Riik/led-matrix/v2/raspberrypi/inc/frameLimiter.hpp

#ifndef FRAMELIMITER_HPP
#define FRAMELIMITER_HPP

#include <chrono>

class FrameLimiter {
    public:
        /* zero is a special case, in that case there will be no sleeping. */
        FrameLimiter(uint_fast32_t framesPerSecond);

        /* Puts the calling thread to sleep until the next frame. */
        void waitForNextFrame();

    private:
        std::chrono::time_point<std::chrono::steady_clock> lastWakeTime;
        std::chrono::nanoseconds timePerFrame;
};

#endif //FRAMELIMITER_HPP
