Riik/led-matrix/v2/raspberrypi/inc/matrixScreen.hpp

#ifndef MATRIXSCREEN_HPP
#define MATRIXSCREEN_HPP
#include <vector>

#include "pixelColor.hpp"

/**
 * The bottom-left is coordinate 0,0.
 */
class MatrixScreen {

    public:
        static constexpr std::size_t matrixPixelCountWidth = 8;
        static constexpr std::size_t matrixPixelCountHeight = 8;

        explicit MatrixScreen(const std::size_t& matrixCountWidth, const std::size_t& matrixCountHeight);

        std::size_t getMatrixCountWidth() const;
        std::size_t getMatrixCountHeight() const;
        std::size_t getPixelCountWidth() const;
        std::size_t getPixelCountHeight() const;

        void resetScreen(PixelColor color);

        PixelColor operator()(std::size_t width, std::size_t height) const;
        PixelColor& operator()(std::size_t width, std::size_t height);

        bool operator==(const MatrixScreen& other) const;
        bool operator!=(const MatrixScreen& other) const;

    private:
        std::vector<PixelColor> screen;
        std::size_t matrixCountWidth;
        std::size_t matrixCountHeight;
        std::size_t pixelCountWidth;
        std::size_t pixelCountHeight;
};
#endif //MATRIXSCREEN_HPP
